TucoFlyer/Winchbot-CAD/references/Load Cell 5kg YZC-133 v8.step

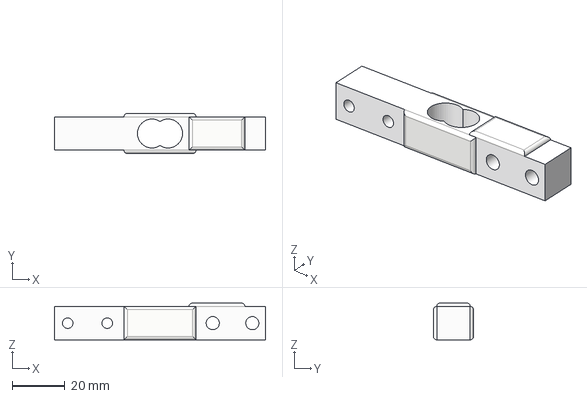
[picture p16: CAD file, 2017-04-28]
references/Load Cell 5kg YZC-133 v8.step
80.0 x 15.2 x 13.9 mm
