TucoFlyer/Winchbot-CAD/bot/winchbot-eframe-powerside-1.stl

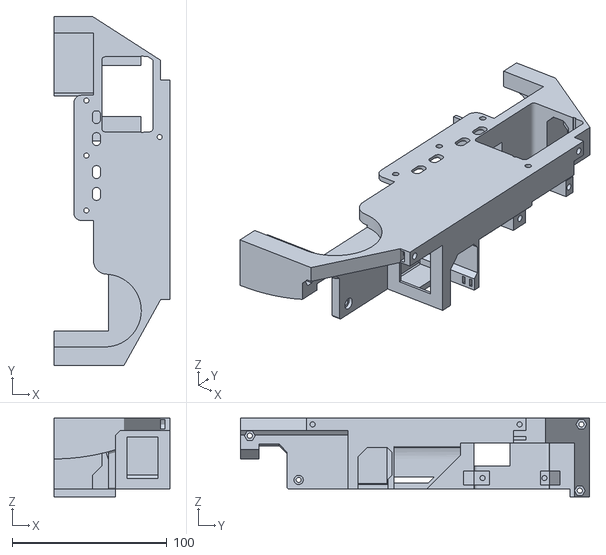
[picture p17: CAD file, 2017-07-24]
bot/winchbot-eframe-powerside-1.stl
74.9 x 225.5 x 50.8
