TucoFlyer/Winchbot-CAD/references/606 v2.step

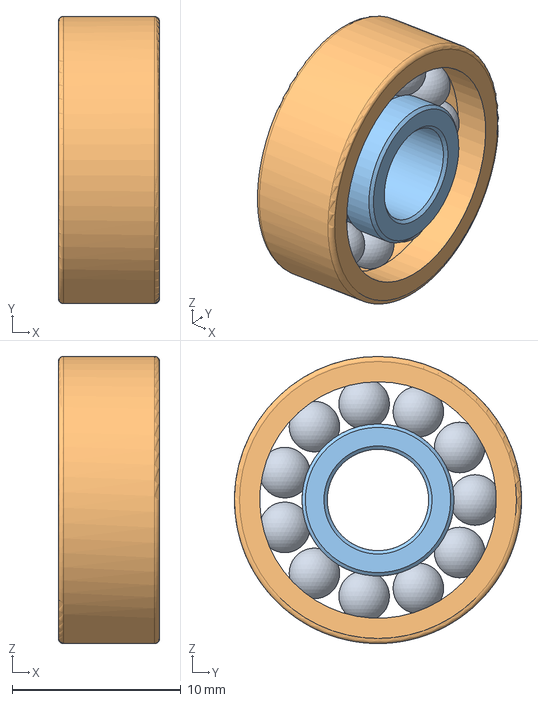
[picture p18: CAD file, 2017-04-28]
references/606 v2.step
6.00 x 17.0 x 17.0 mm
