TucoFlyer/Winchbot-CAD/bot/winchbot-topbracket-2.stp

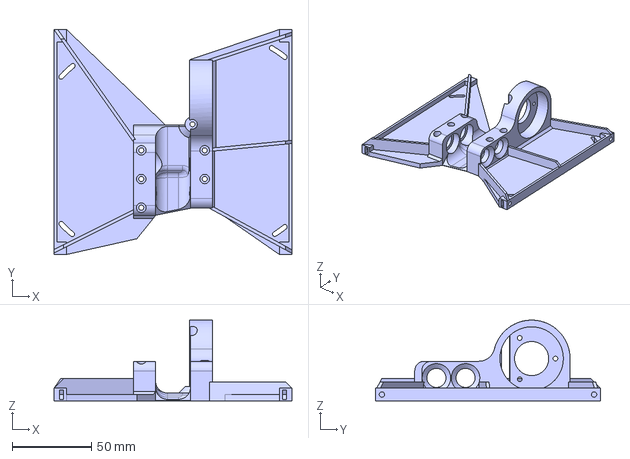
[picture p19: CAD file, 2017-07-23]
bot/winchbot-topbracket-2.stp
150.0 x 141.7 x 50.9 mm
