TucoFlyer/Winchbot-CAD/references/Shaft Encoder 38mm v5.step

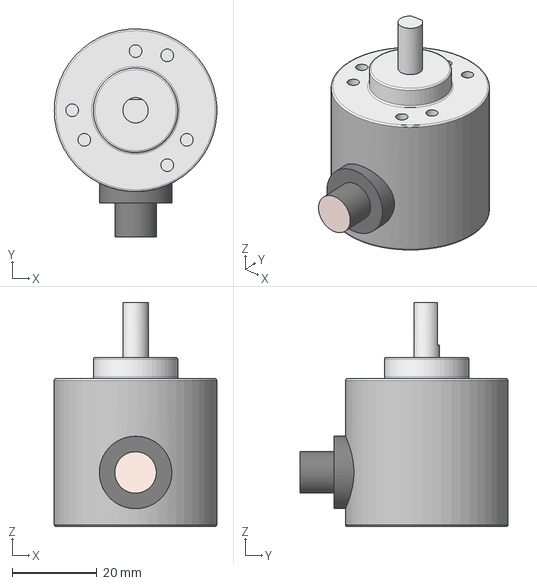
[picture p20: CAD file, 2017-04-28]
references/Shaft Encoder 38mm v5.step
38.5 x 49.2 x 53.0 mm
