TucoFlyer/Winchbot-CAD/bot/extpulley-spacer-1.stl

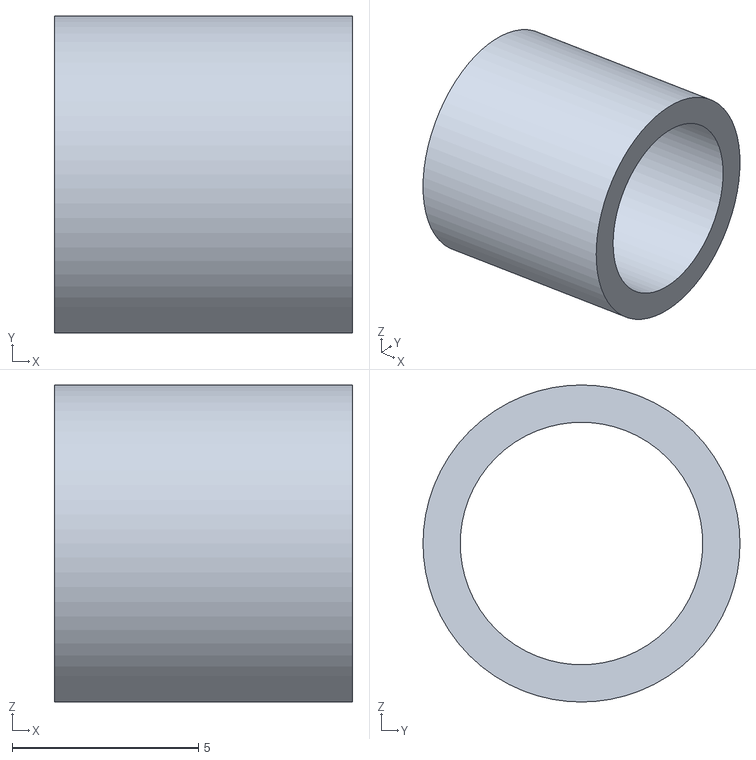
[picture p21: CAD file, 2017-07-20]
bot/extpulley-spacer-1.stl
8.00 x 8.50 x 8.50
