TucoFlyer/Winchbot-CAD/bot/winchbot-shortroller-3.stl

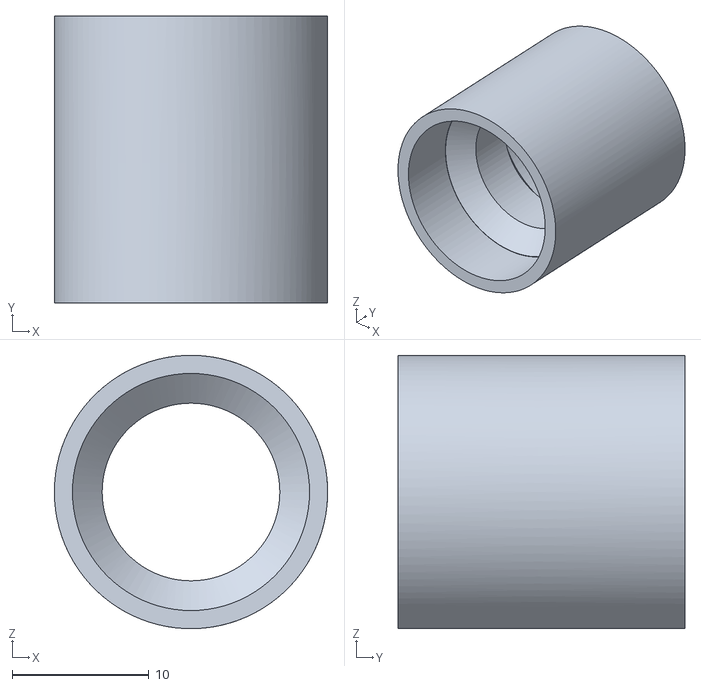
[picture p22: CAD file, 2017-07-20]
bot/winchbot-shortroller-3.stl
20.0 x 21.0 x 20.0
