TucoFlyer/Winchbot-CAD/bot/winchbot-shortrtube-3.stl

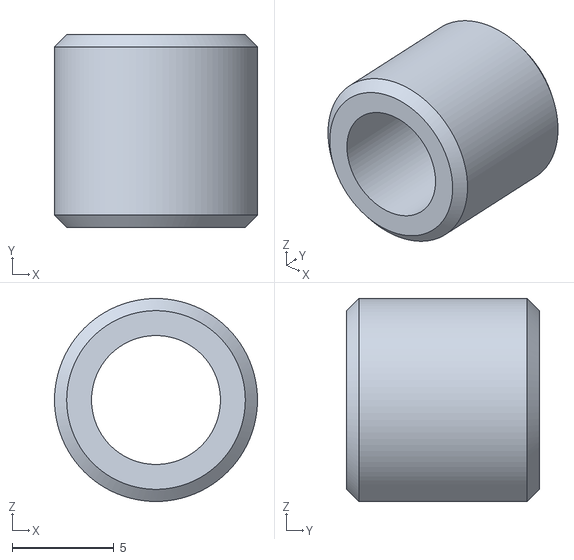
[picture p23: CAD file, 2017-07-20]
bot/winchbot-shortrtube-3.stl
10.0 x 9.50 x 10.0
