TucoFlyer/Winchbot-CAD/bot/extpulley-frameA-1.stl

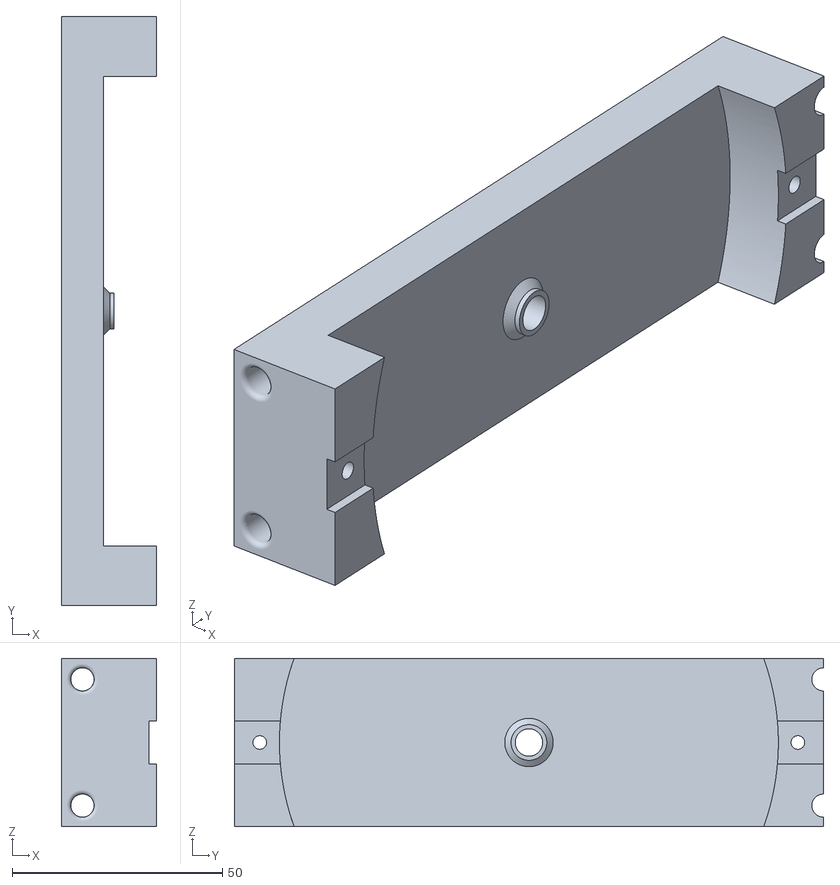
[picture p24: CAD file, 2017-07-20]
bot/extpulley-frameA-1.stl
22.6 x 140.0 x 40.0
