TucoFlyer/Winchbot-CAD/bot/extpulley-frameB-1.stl

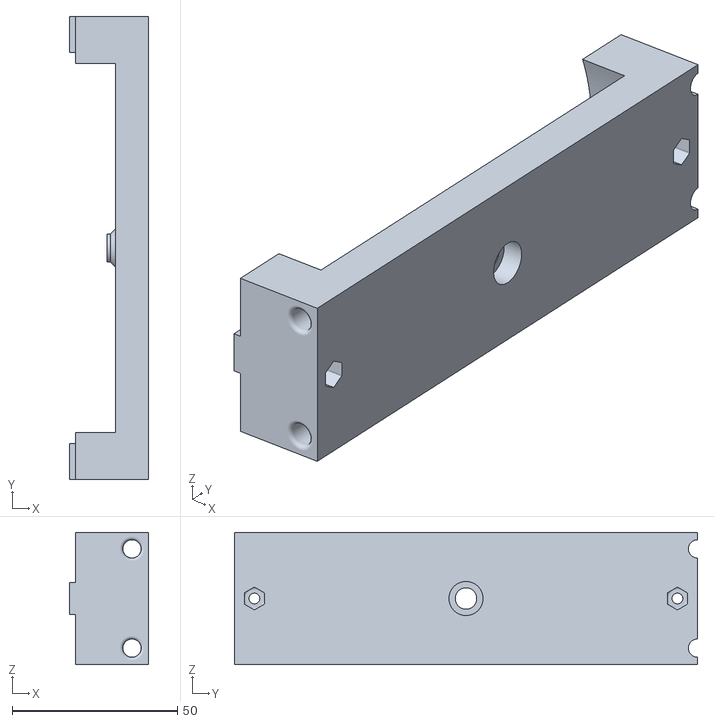
[picture p25: CAD file, 2017-07-20]
bot/extpulley-frameB-1.stl
23.9 x 140.0 x 40.0
