TucoFlyer/Winchbot-CAD/bot/winchbot-toproll-3.stl

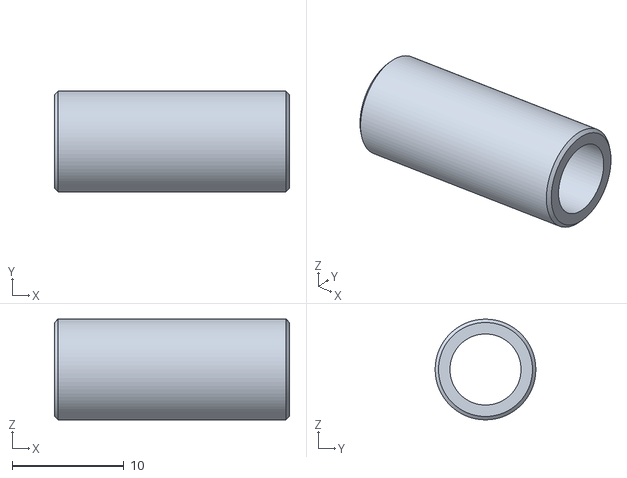
[picture p26: CAD file, 2017-07-11]
bot/winchbot-toproll-3.stl
21.0 x 9.00 x 9.00
