TucoFlyer/Winchbot-CAD/bot/winchbot-loadcell-bracket-1.stl

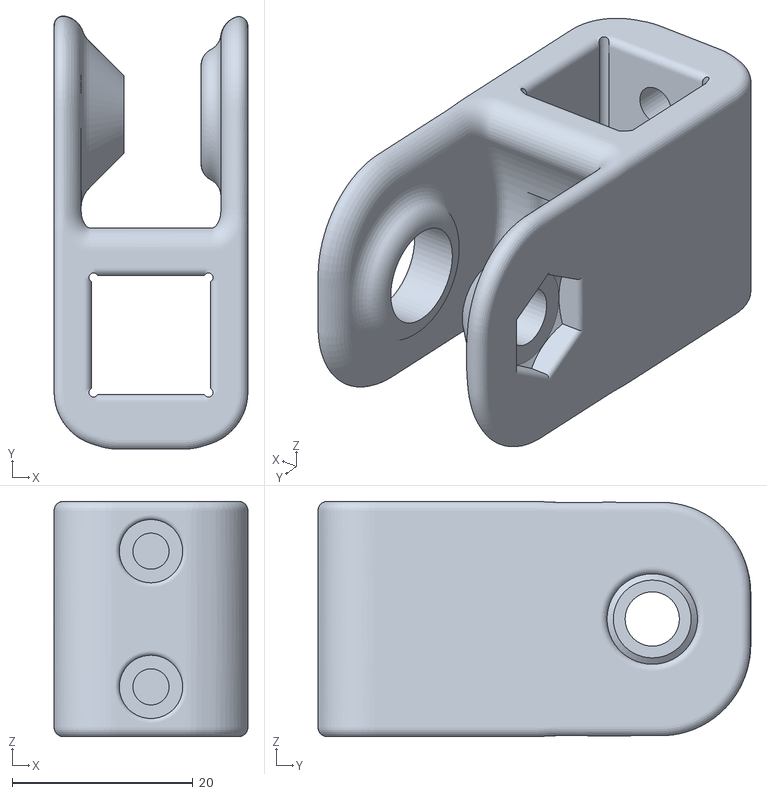
[picture p27: CAD file, 2017-07-11]
bot/winchbot-loadcell-bracket-1.stl
21.4 x 47.9 x 26.0
