TucoFlyer/Winchbot-CAD/bot/winchbot-spool-core-3.stl

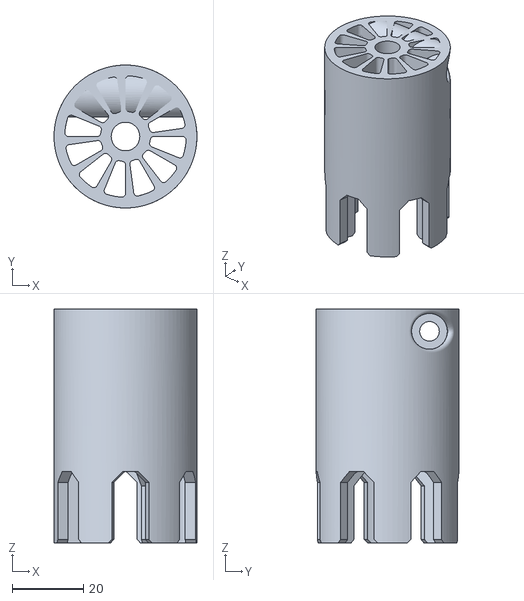
[picture p28: CAD file, 2017-07-07]
bot/winchbot-spool-core-3.stl
40.0 x 40.0 x 65.5
