TucoFlyer/Winchbot-CAD/bot/winchbot-spool-driveside-3.stl

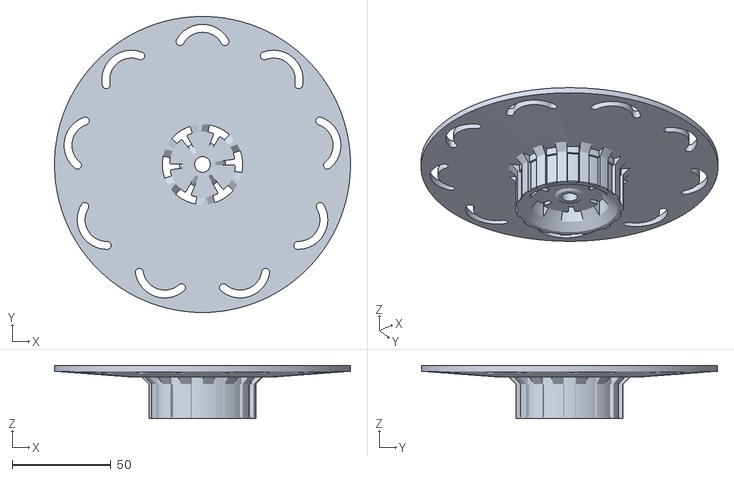
[picture p29: CAD file, 2017-07-07]
bot/winchbot-spool-driveside-3.stl
150.0 x 150.0 x 27.0
