TucoFlyer/Winchbot-CAD/bot/Spool.step

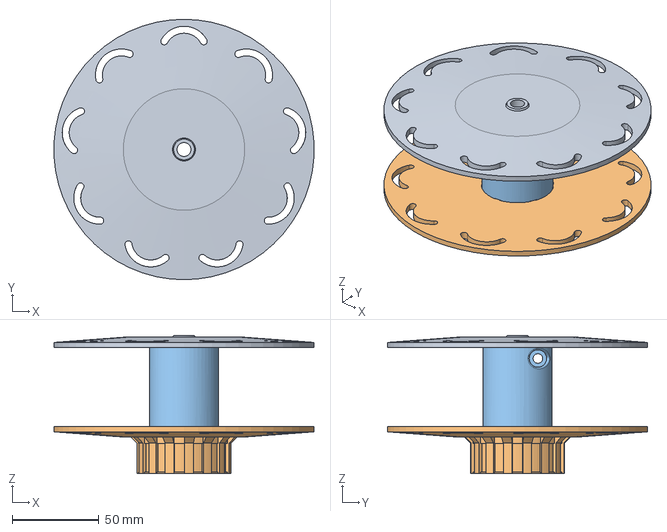
[picture p30: CAD file, 2017-07-07]
bot/Spool.step
149.8 x 150.0 x 79.5 mm
