TucoFlyer/Winchbot-CAD/bot/winchbot-spool-idlerside-3.stl

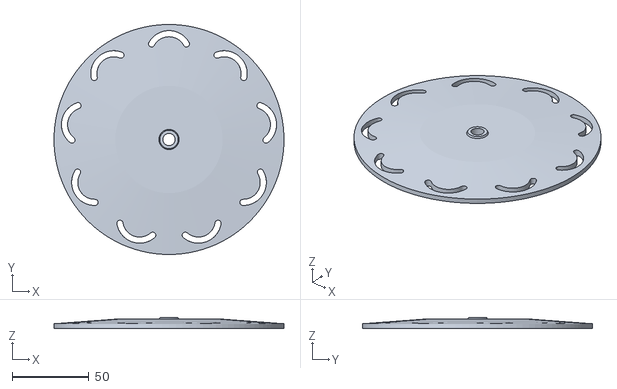
[picture p31: CAD file, 2017-07-07]
bot/winchbot-spool-idlerside-3.stl
150.0 x 150.0 x 7.00
