TucoFlyer/Winchbot-CAD/bot/winchbot-frame-idlerhalf-4.stl

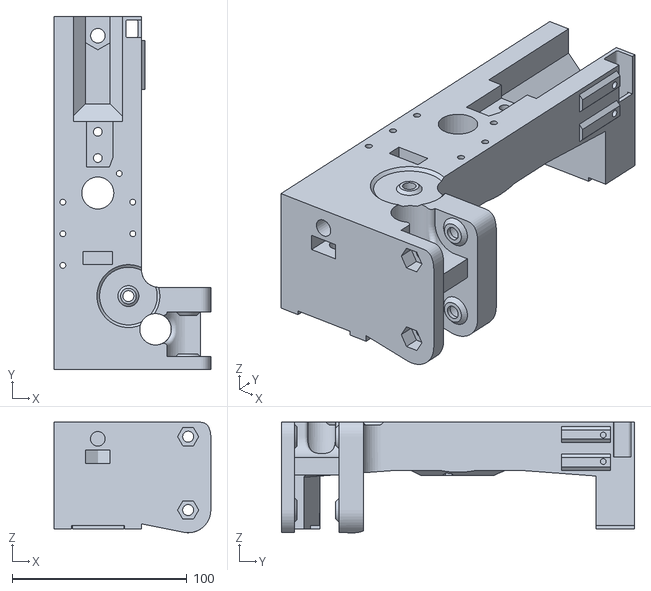
[picture p32: CAD file, 2017-07-01]
bot/winchbot-frame-idlerhalf-4.stl
89.7 x 202.0 x 63.2
