TucoFlyer/Winchbot-CAD/bot/winchbot-frame-drivehalf-4.stl

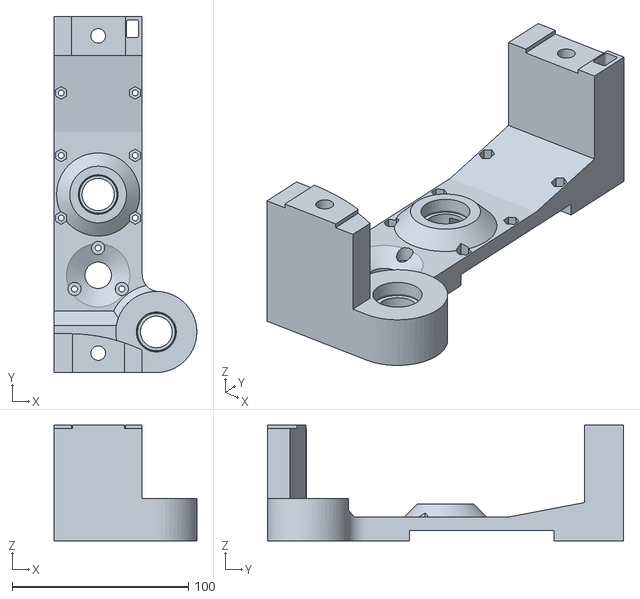
[picture p33: CAD file, 2017-07-01]
bot/winchbot-frame-drivehalf-4.stl
81.0 x 202.0 x 65.8
