TucoFlyer/Winchbot-CAD/bot/winchbot-motor-flexgear-2.stl

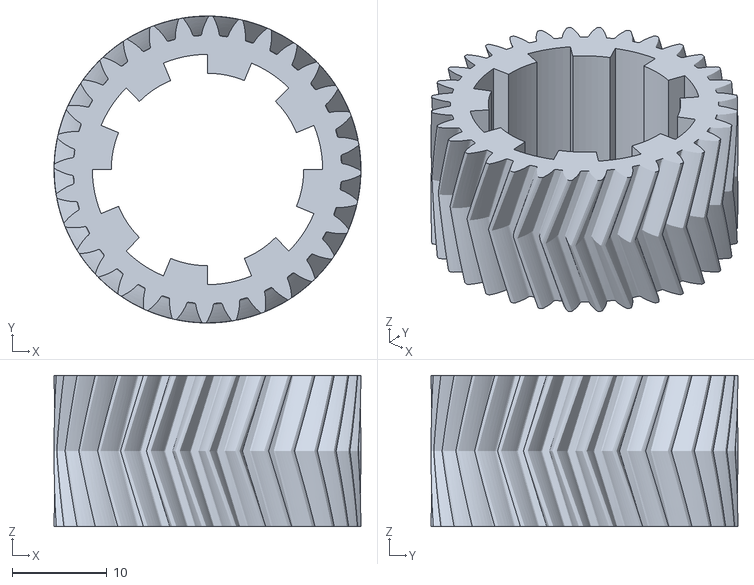
[picture p34: CAD file, 2017-06-27]
bot/winchbot-motor-flexgear-2.stl
32.5 x 32.5 x 16.0
