TucoFlyer/Winchbot-CAD/bot/winchbot-motor-hub-2.stl

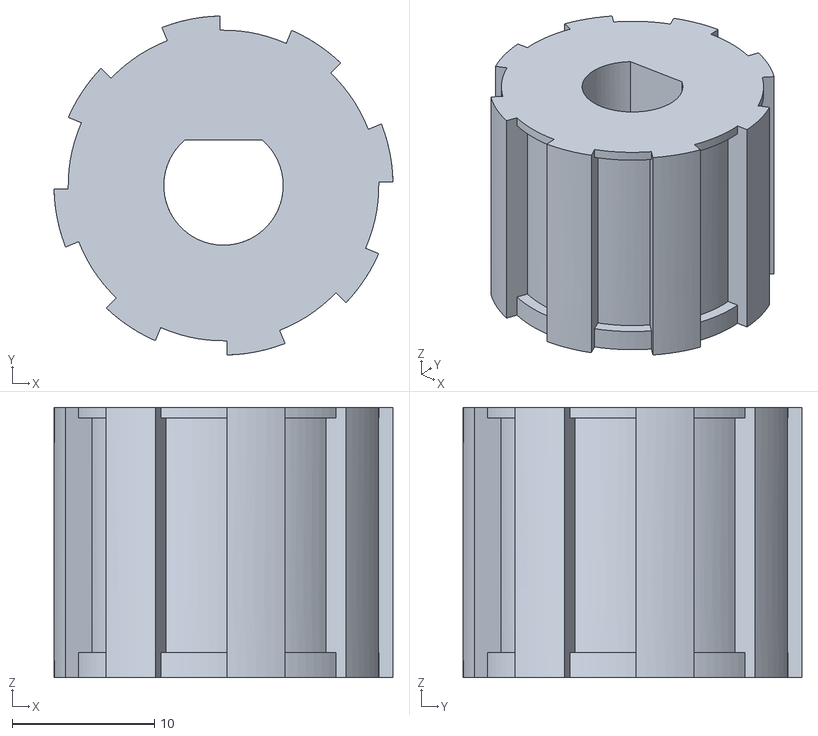
[picture p35: CAD file, 2017-06-27]
bot/winchbot-motor-hub-2.stl
23.9 x 23.9 x 19.0
