TucoFlyer/Winchbot-CAD/bot/winchbot-flatroller-1.stl

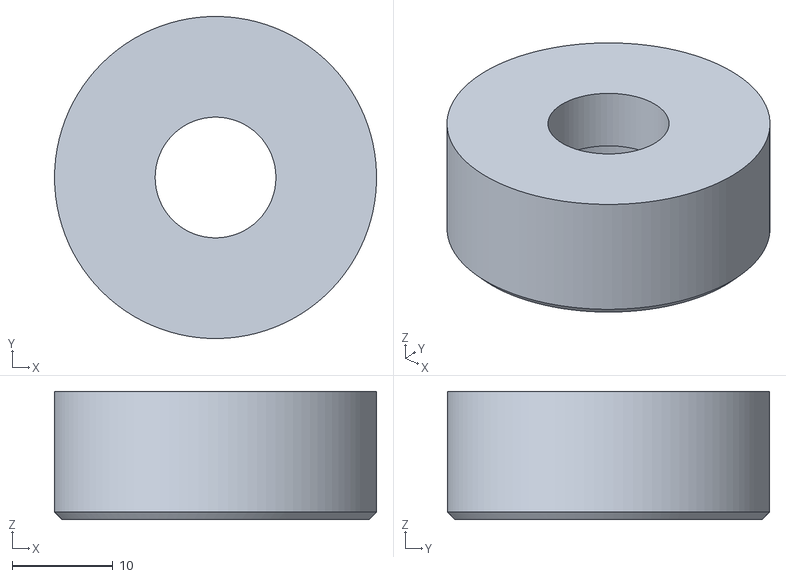
[picture p36: CAD file, 2017-06-27]
bot/winchbot-flatroller-1.stl
32.0 x 32.0 x 12.8
