TucoFlyer/Winchbot-CAD/bot/winchbot-spool-flexgear-2.stl

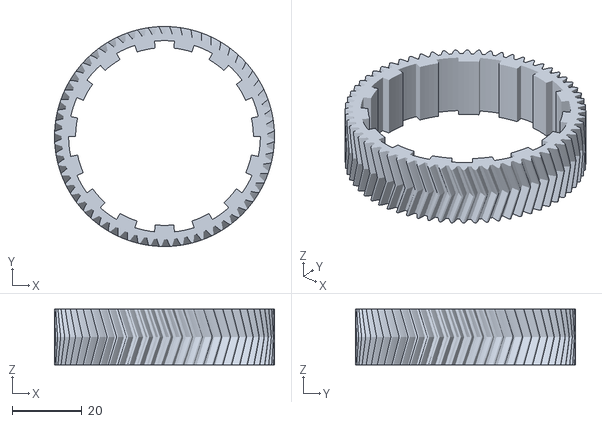
[picture p37: CAD file, 2017-06-27]
bot/winchbot-spool-flexgear-2.stl
63.0 x 63.0 x 16.0
