TucoFlyer/Winchbot-CAD/bot/winchbot-small-idler.stl

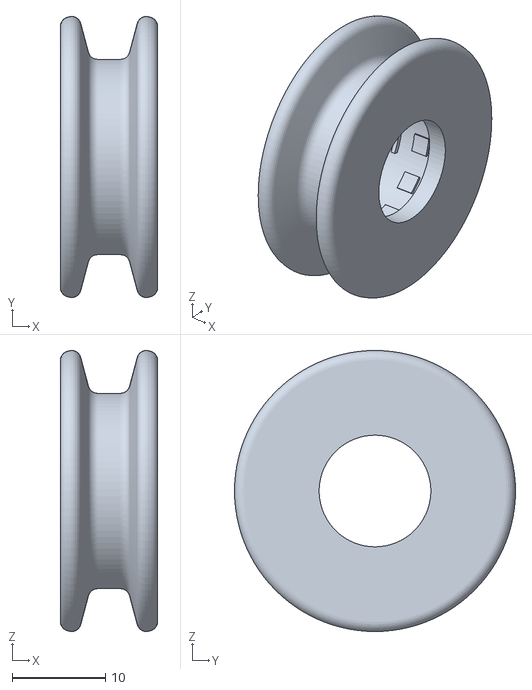
[picture p38: CAD file, 2017-04-28]
bot/winchbot-small-idler.stl
10.5 x 30.2 x 30.2
