TucoFlyer/Winchbot-CAD/bot/winchbot-encoder-capstan.stl

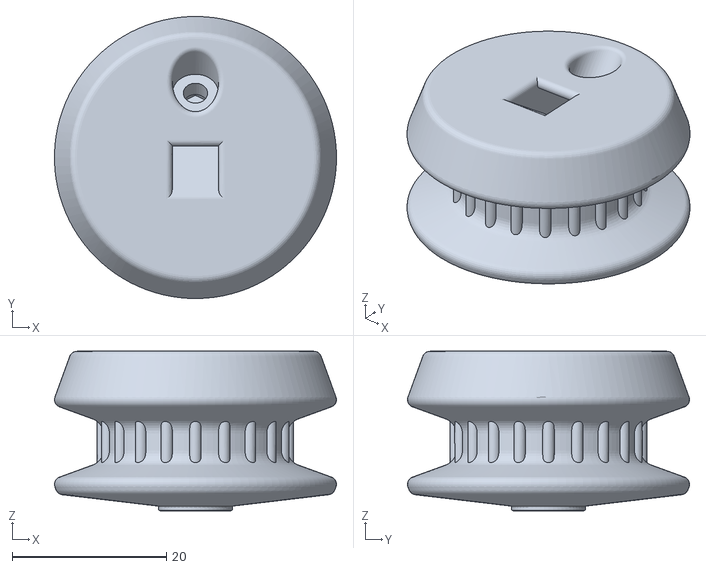
[picture p39: CAD file, 2017-04-28]
bot/winchbot-encoder-capstan.stl
36.6 x 36.6 x 20.7
